CarlosGS/OpenBinaural/Electronics/misc/amplifier_circuit_by_MatthewLai.jpg

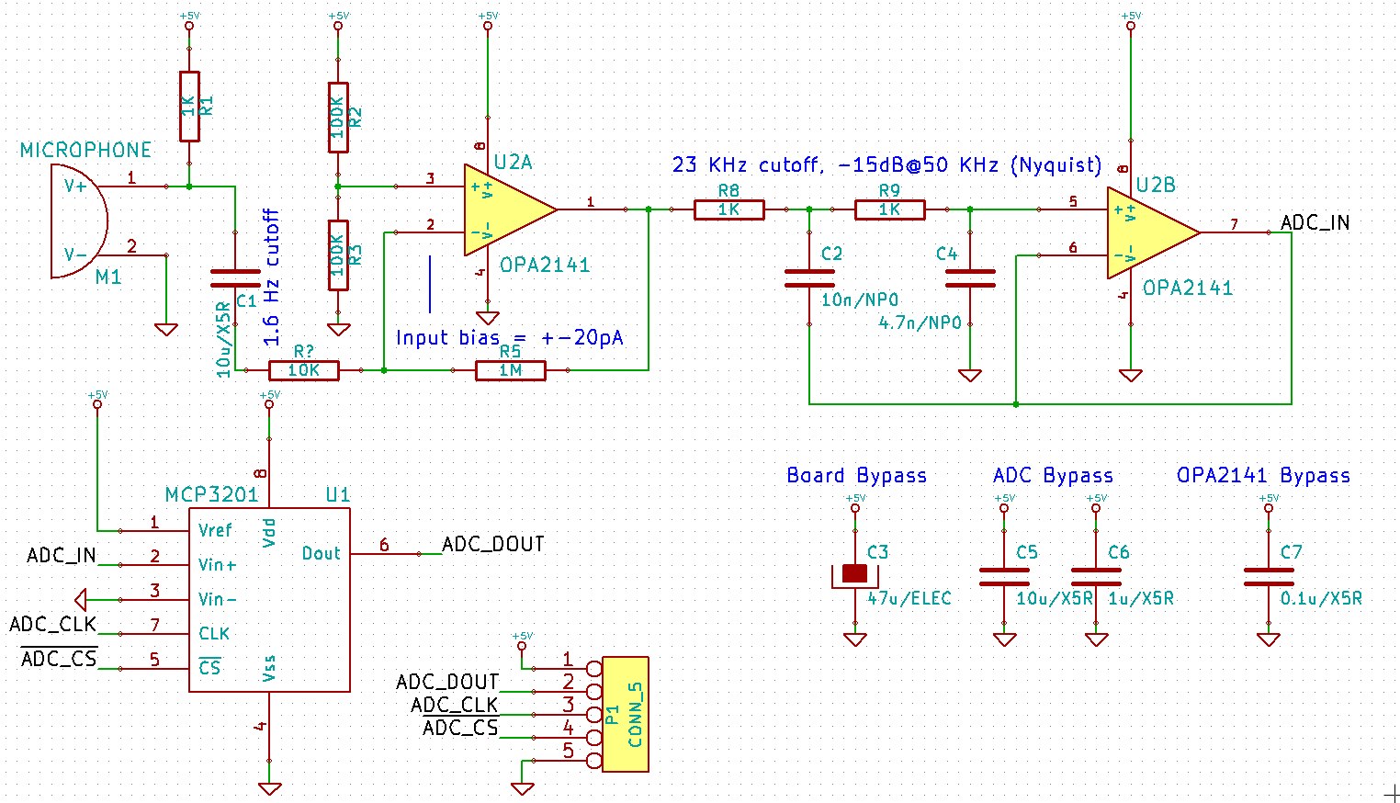
Electronics/misc/amplifier_circuit_by_MatthewLai.jpg
