CarlosGS/OpenBinaural/Electronics/misc/texasInstruments_diagram.png

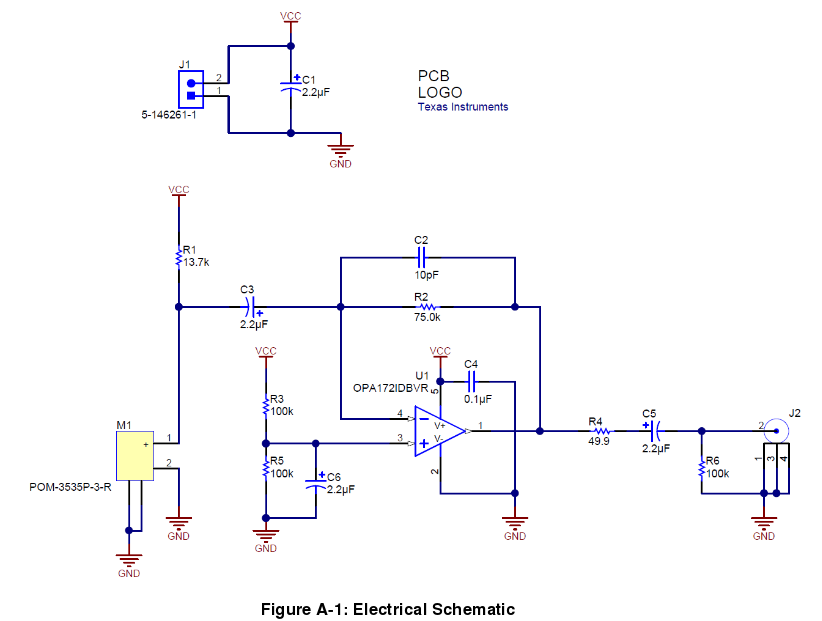
Electronics/misc/texasInstruments_diagram.png
