CarlosGS/OpenBinaural/Electronics/pictures/mic_polarity.jpg

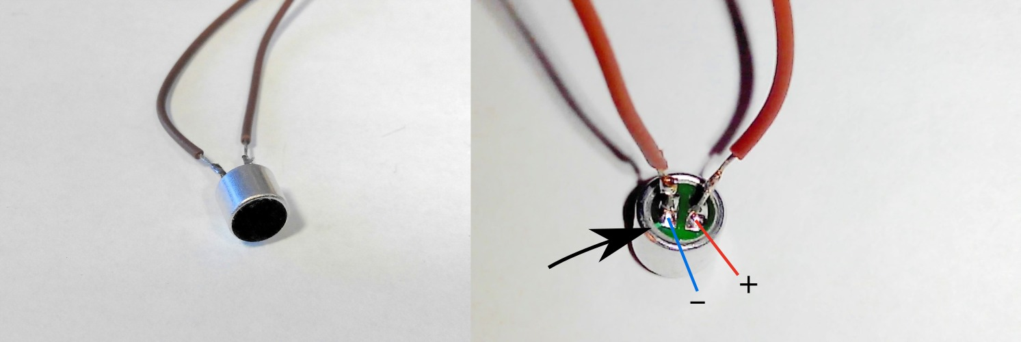
Electronics/pictures/mic_polarity.jpg
