CarlosGS/OpenBinaural/pictures/GoPro_pins_In_for_stereo_audio_by_Philippe_Benaim.jpg

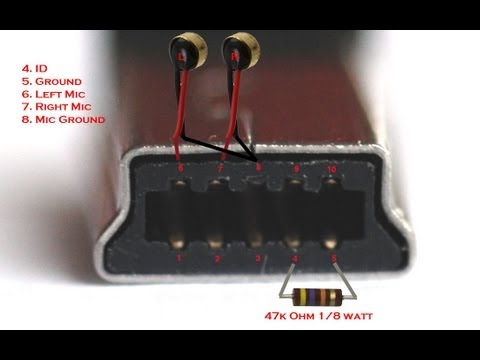
pictures/GoPro_pins_In_for_stereo_audio_by_Philippe_Benaim.jpg
