CarlosGS/OpenBinaural/pictures/mic_placement.jpg

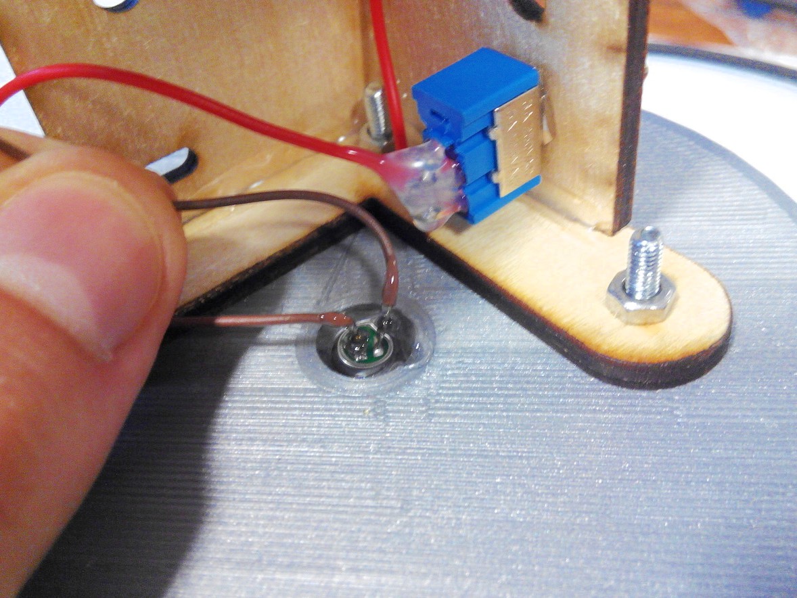
pictures/mic_placement.jpg
