CarlosGS/OpenBinaural/pictures/OpenBinaural_GoPro_by_Philippe_Benaim.jpg

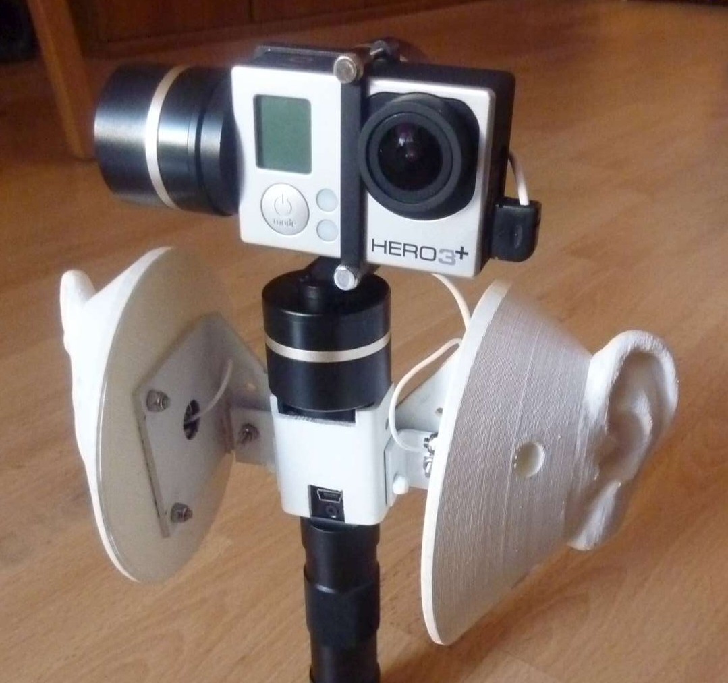
pictures/OpenBinaural_GoPro_by_Philippe_Benaim.jpg
