CarlosGS/OpenBinaural/pictures/wood_support.png

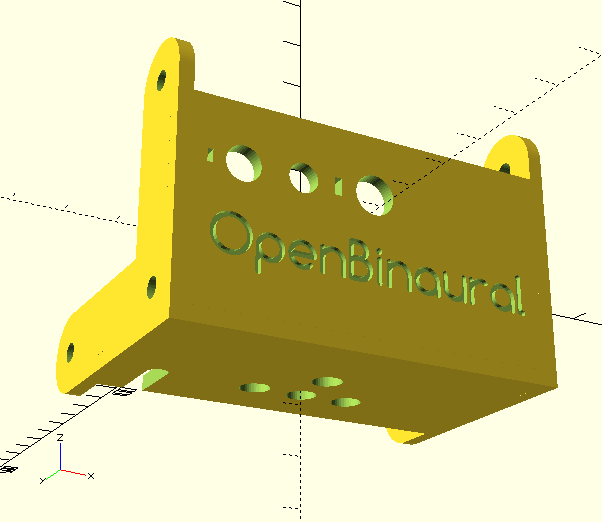
pictures/wood_support.png
