CarlosGS/OpenBinaural/Electronics/misc/components.jpg

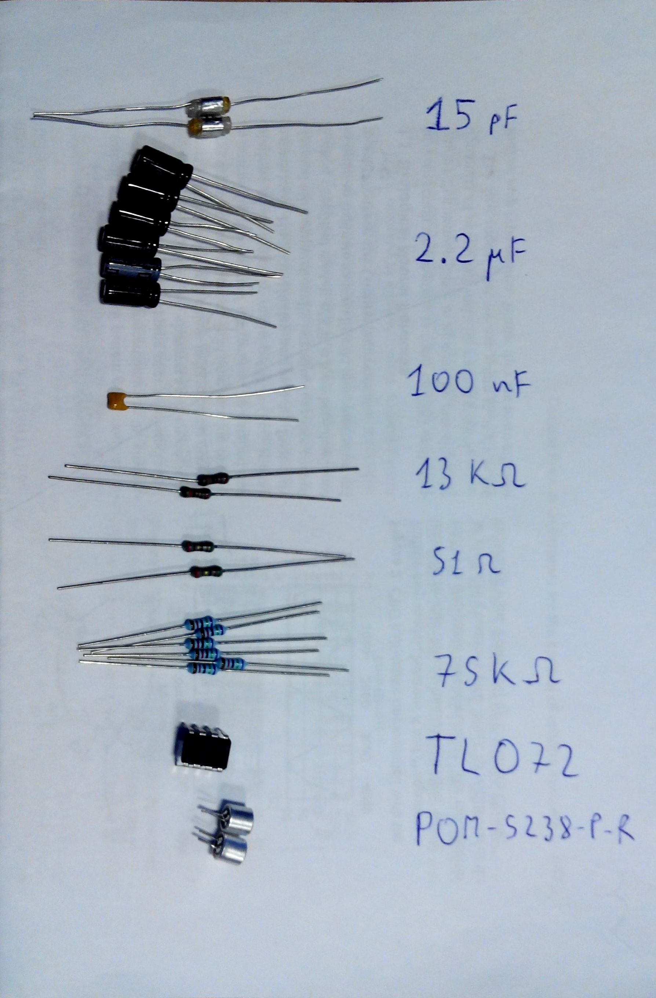
Electronics/misc/components.jpg
